ikesato/autowater/doc/images/IMG_0155.jpg

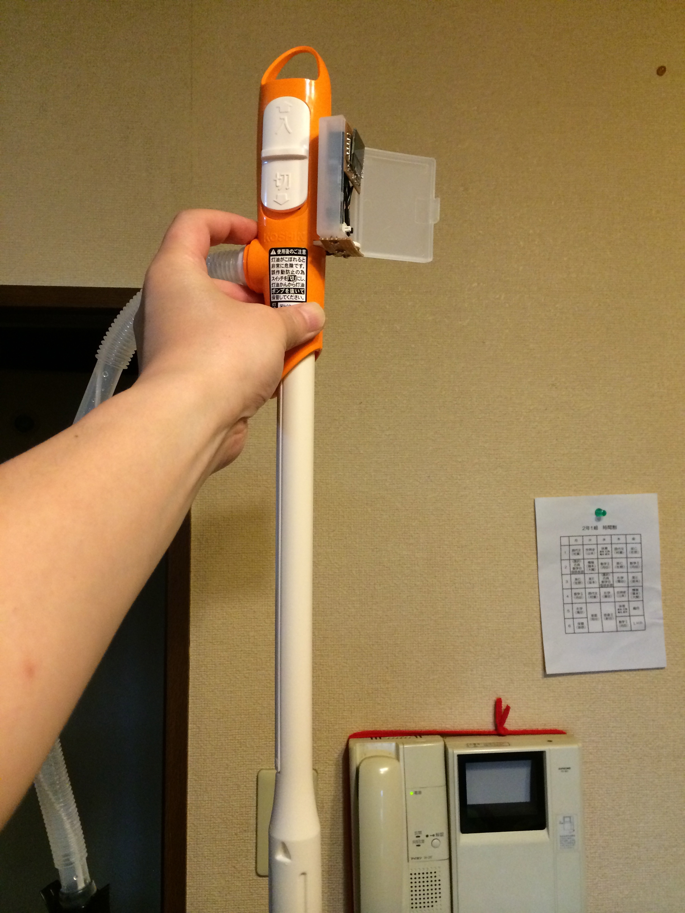
doc/images/IMG_0155.jpg
