ikesato/autowater/doc/images/IMG_0221.JPG

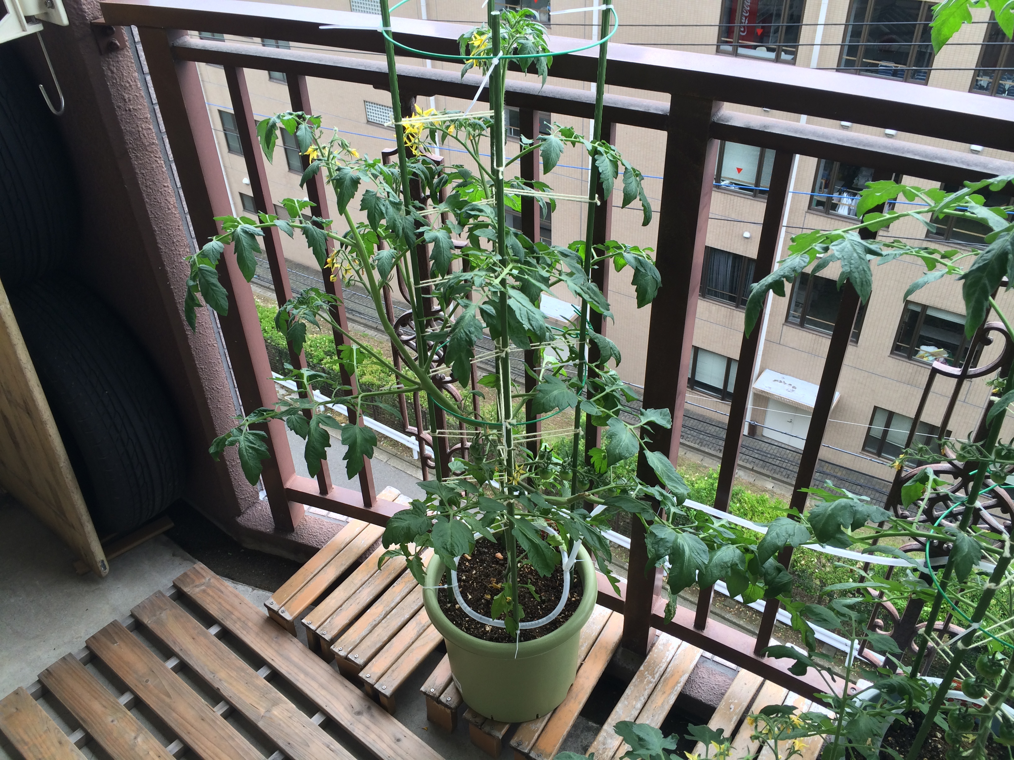
doc/images/IMG_0221.JPG
