ikesato/autowater/doc/images/IMG_0223.JPG

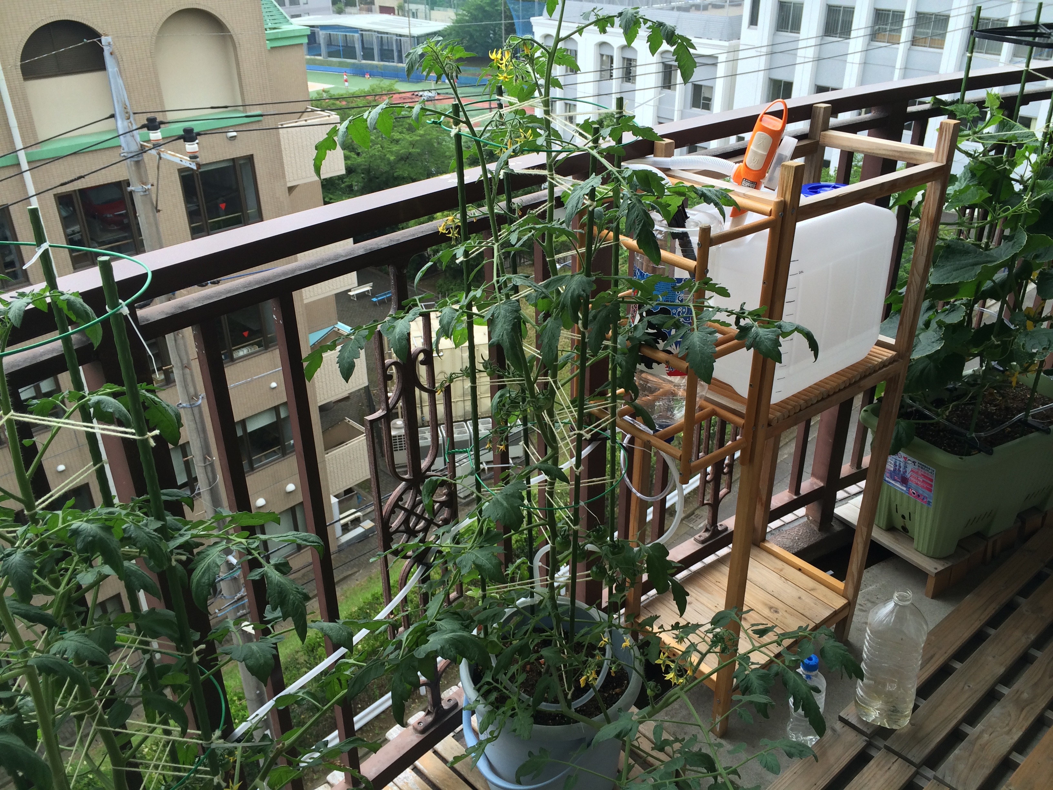
doc/images/IMG_0223.JPG
