ikesato/autowater/doc/images/IMG_0225.JPG

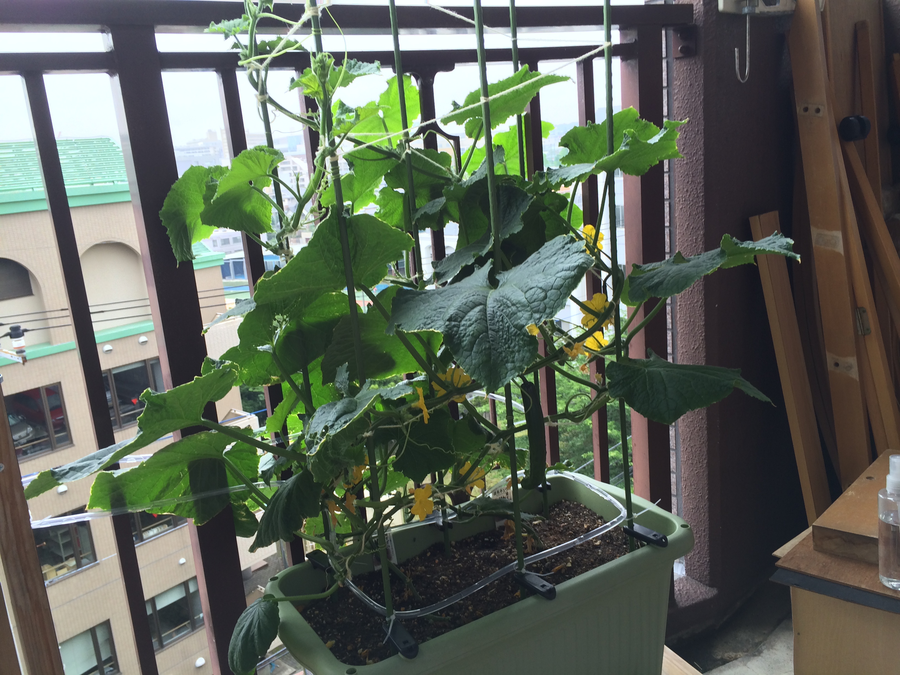
doc/images/IMG_0225.JPG
