ikesato/autowater/doc/images/IMG_0227.JPG

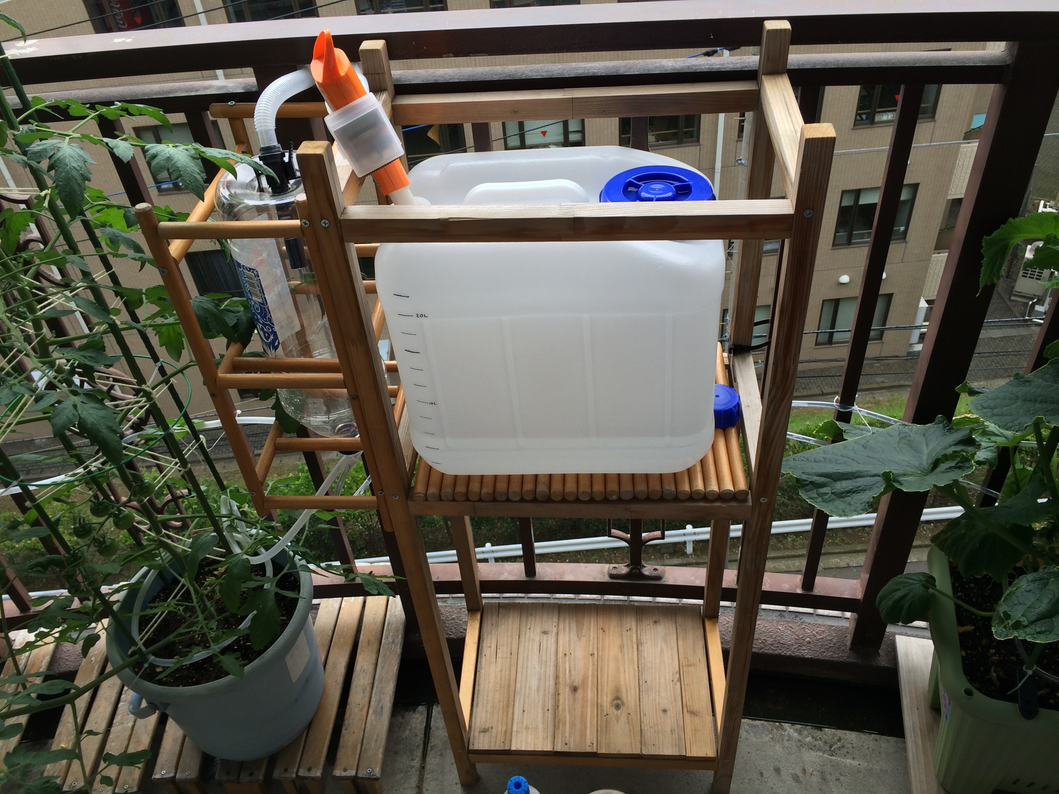
doc/images/IMG_0227.JPG
