ikesato/autowater/autowater.X/i2c.c

/******************************************************************************
 * Copyright (c) 2014 Satoshi Ikeda
 *
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
 * THE SOFTWARE IS PROVIDED "AS IS", WITHOUT WARRANTY OF ANY KIND, EXPRESS OR
 * IMPLIED, INCLUDING BUT NOT LIMITED TO THE WARRANTIES OF MERCHANTABILITY,
 * FITNESS FOR A PARTICULAR PURPOSE AND NONINFRINGEMENT. IN NO EVENT SHALL THE
 * AUTHORS OR COPYRIGHT HOLDERS BE LIABLE FOR ANY CLAIM, DAMAGES OR OTHER
 * LIABILITY, WHETHER IN AN ACTION OF CONTRACT, TORT OR OTHERWISE, ARISING FROM,
 * OUT OF OR IN CONNECTION WITH THE SOFTWARE OR THE USE OR OTHER DEALINGS IN
 * THE SOFTWARE.
 *****************************************************************************/

/**
 * Note:
 * - This codes use 8MHz for CPU clock.
 *   If you change clock, change SSP1ADD value.
 * - i2c speed is 100KHz
 */

#include <xc.h>
#include "i2c.h"

int ack_flag;

/**
 * !@brief Check the idle status
 *
 * Escape this function when ACKEN, RCEN, PEN, RSEN, SEN, R/W and BF registers
 * were all zero.
 * @param[in] mask Mask for SSP1STAT register
 */
void i2c_check_idle(char mask)
{
    while ((SSP1CON2 & 0x1F ) | (SSP1STAT & mask));
}

/**
 * !@brief Interrupt fucntion for i2c
 *
 * Call this function from global interrupt function in main.c.
 */
void i2c_interrupt(void)
{
    if (SSP1IF == 1) {
        if (ack_flag == 1) {
          ack_flag = 0;
        }
        SSP1IF = 0;
    }
    if (BCL1IF == 1) {
        BCL1IF = 0;         // Clear only
    }
}

/**
 * !@brief Initialize as i2c master
 *
 * Note: This codes use 8MHz for CPU clock.
 *       If you change clock, change SSP1ADD value.
 */
void i2c_init_master(void)
{
    SSP1STAT= 0b10000000;   // normal speed, 100kHz.
    SSP1CON1= 0b00101000;   // master mode
    SSP1ADD = 0x13;         // clock=FOSC/((SSPADD + 1)*4)
                            //   => 8MHz/((0x13+1)*4)=0.1(100KHz)

    SSP1IE = 1;             // Enable SSP(I2C) interrupt
    BCL1IE = 1;             // Enable MSSP(I2C) conflict interrupt
    PEIE   = 1;             // Enable Peripheral interrupt
    GIE    = 1;             // Enable Global interrupt
    SSP1IF = 0;             // Clear SSP(I2C) interrupt flag
    BCL1IF = 0;             // Clear MSSP(I2C) interrupt flag
}

/**
 * !@brief Send start condition to slave
 *
 * @param[in] adrs Slave address
 * @param[in] rw 0:write 1:read
 * @return Return the result. 0:success 1:failure
 */
int i2c_start(int adrs, int rw)
{
    // Set start condition
    i2c_check_idle(0x5);
    SSP1CON2bits.SEN = 1;

    // Set slave address and rw mode
    i2c_check_idle(0x5);
    ack_flag = 1;
    SSP1BUF = (char)((adrs<<1)+rw);
    while (ack_flag);       // Wait ACK
    return SSP1CON2bits.ACKSTAT;
}

/**
 * !@brief Send repeated start condtion command
 *
 * @param[in] adrs Slave address
 * @param[in] rw 0:write 1:read
 * @return Return the result. 0:success 1:failure
 */
int i2c_rstart(int adrs,int rw)
{
    // Set repeated start condition
    i2c_check_idle(0x5);
    SSP1CON2bits.RSEN = 1;

    // Set slave address and rw mode
    i2c_check_idle(0x5);
    ack_flag = 1;
    SSP1BUF = (char)((adrs<<1)+rw);
    while (ack_flag);       // Wait ACK
    return SSP1CON2bits.ACKSTAT;
}

/**
 * !@brief Send stop condition
 */
void i2c_stop(void)
{
    i2c_check_idle(0x5);
    SSP1CON2bits.PEN = 1;
}

/**
 * !@brief Send data
 *
 * @param[in] dt Data to send
 * @return Return the result. 0:success 1:failure
 */
int i2c_send(char dt)
{
    i2c_check_idle(0x5);
    ack_flag = 1;
    SSP1BUF = dt;
    while (ack_flag);       // Wait ACK
    return SSP1CON2bits.ACKSTAT;
}

/**
 * !@brief Receive data from slave
 *
 * @param[in] ack ACK data after received
 * @return Received data
 */
char i2c_receive(int ack)
{
    char dt;

    i2c_check_idle(0x5);
    SSP1CON2bits.RCEN = 1;      // Enable receive
    i2c_check_idle(0x4);
    dt = SSP1BUF;               // Receive data
    i2c_check_idle(0x5);
    SSP1CON2bits.ACKDT = ack;
    SSP1CON2bits.ACKEN = 1;     // Response ACK
    return dt;
}
